Randagodron/hot-silicon-fuzz/export/sig_01_01.PNG

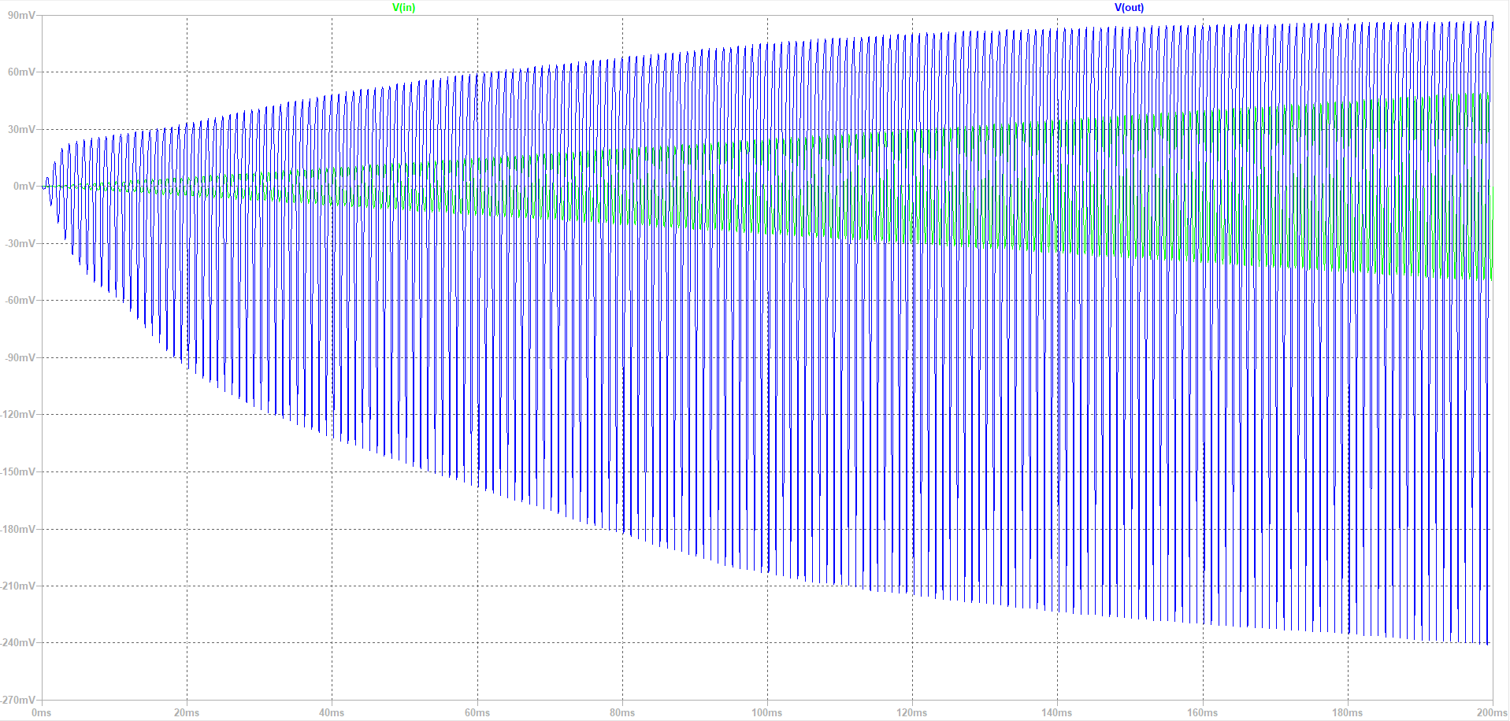
export/sig_01_01.PNG
