Randagodron/hot-silicon-fuzz/export/sig_01_02.PNG

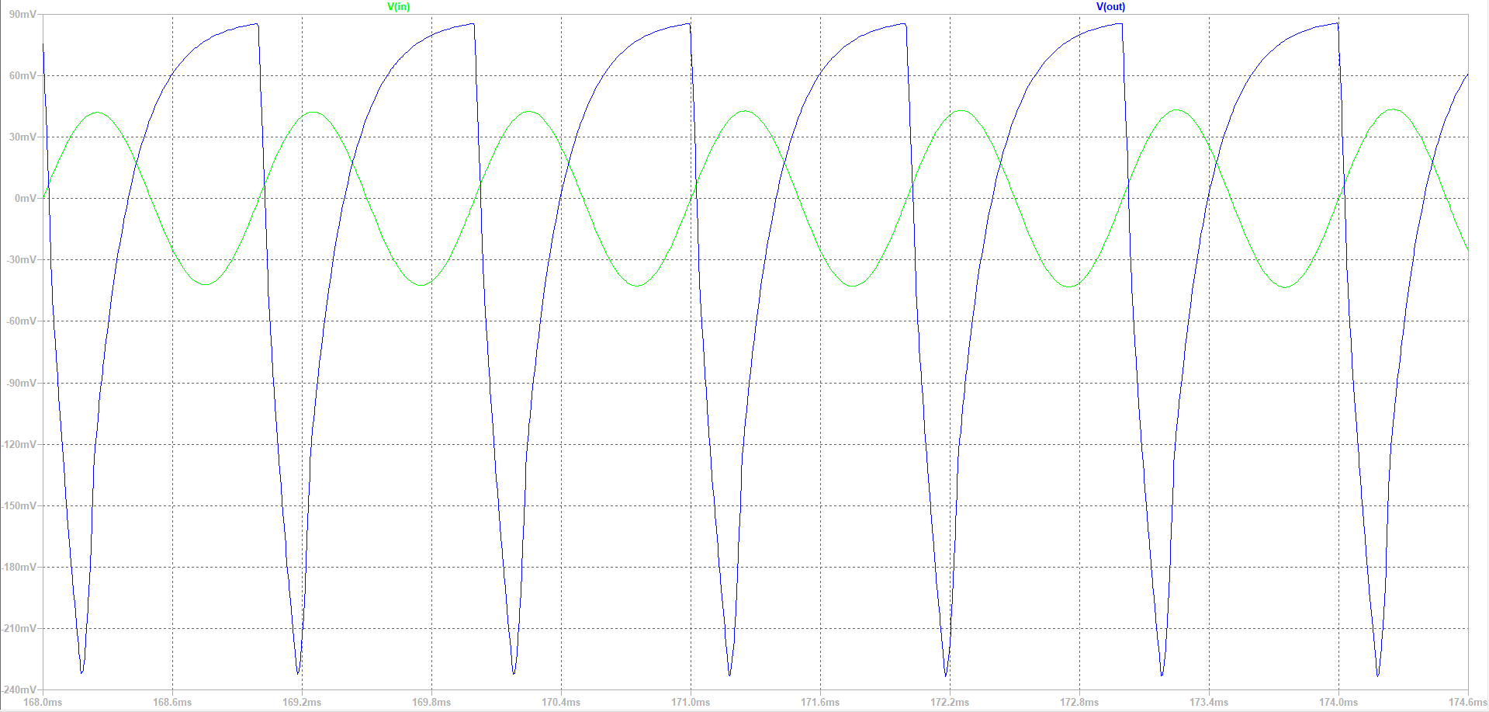
export/sig_01_02.PNG
