Randagodron/hot-silicon-fuzz/export/sig_02_02_bias0.1.PNG

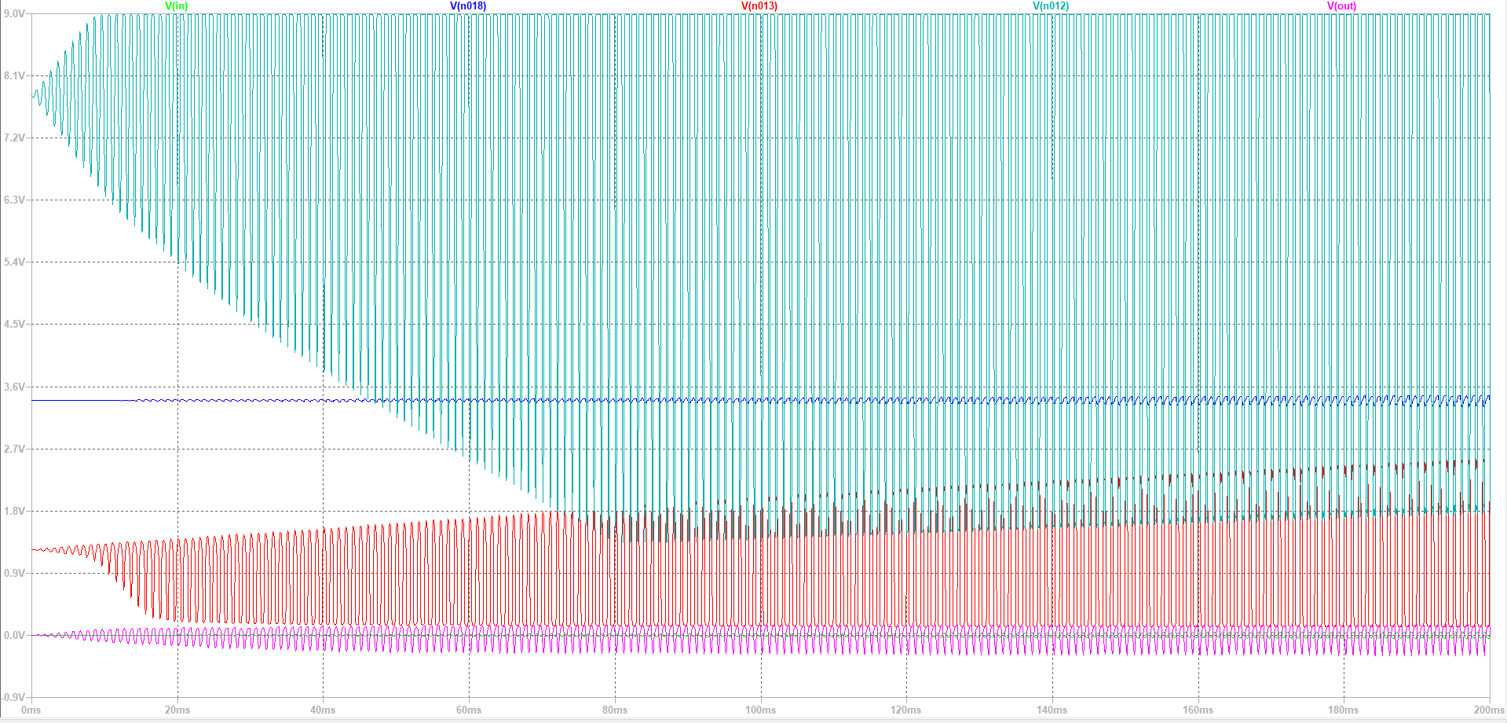
export/sig_02_02_bias0.1.PNG
