Randagodron/hot-silicon-fuzz/export/sig_02_03.PNG

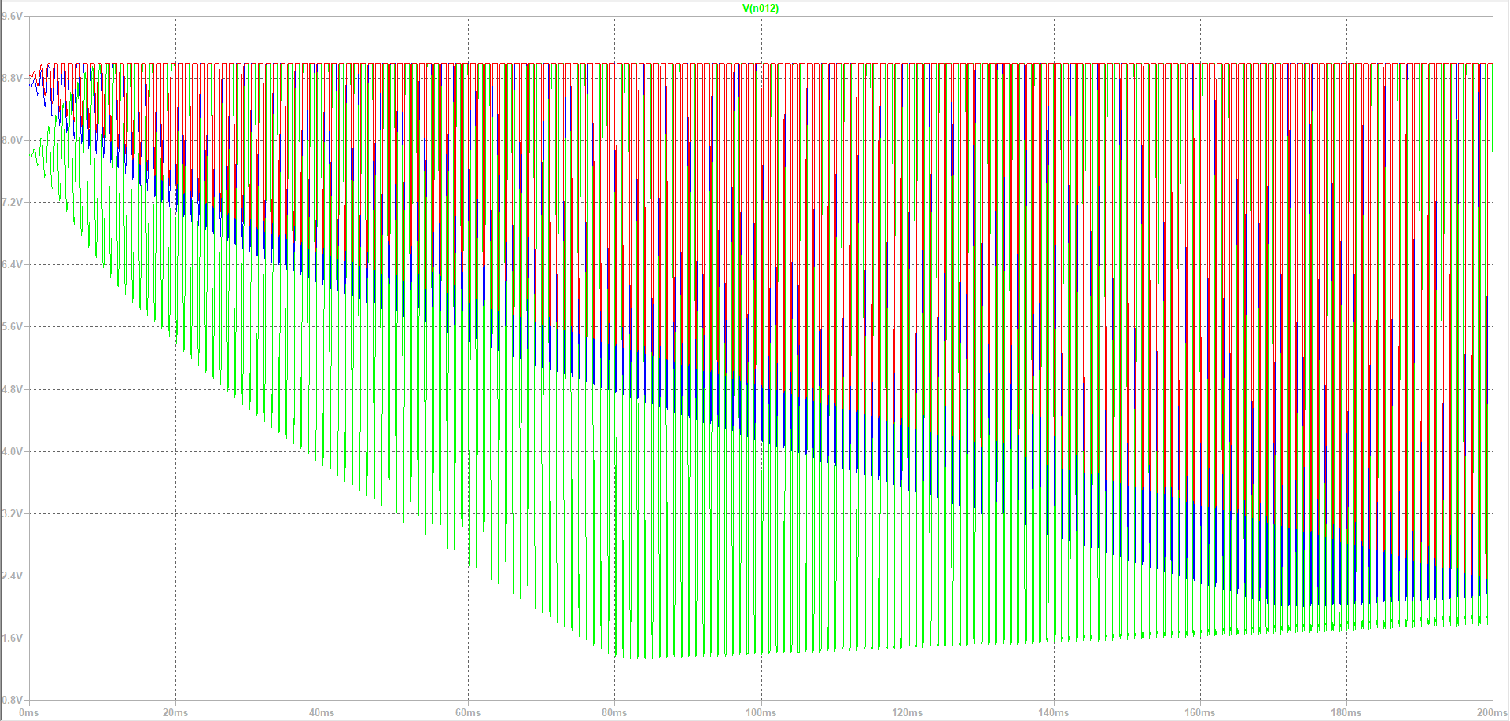
export/sig_02_03.PNG
