Randagodron/hot-silicon-fuzz/export/sig_02_04.PNG

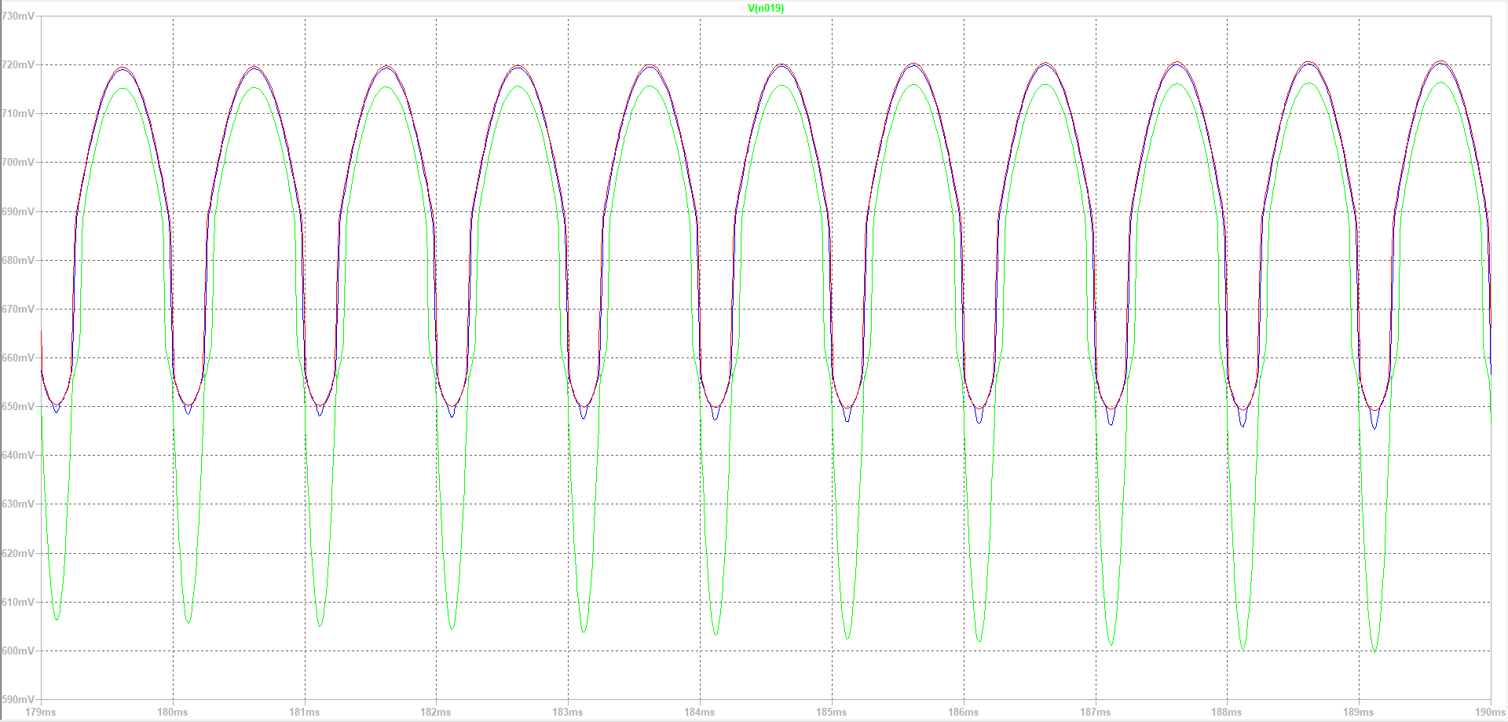
export/sig_02_04.PNG
