Randagodron/hot-silicon-fuzz/export/sig_02_06.PNG

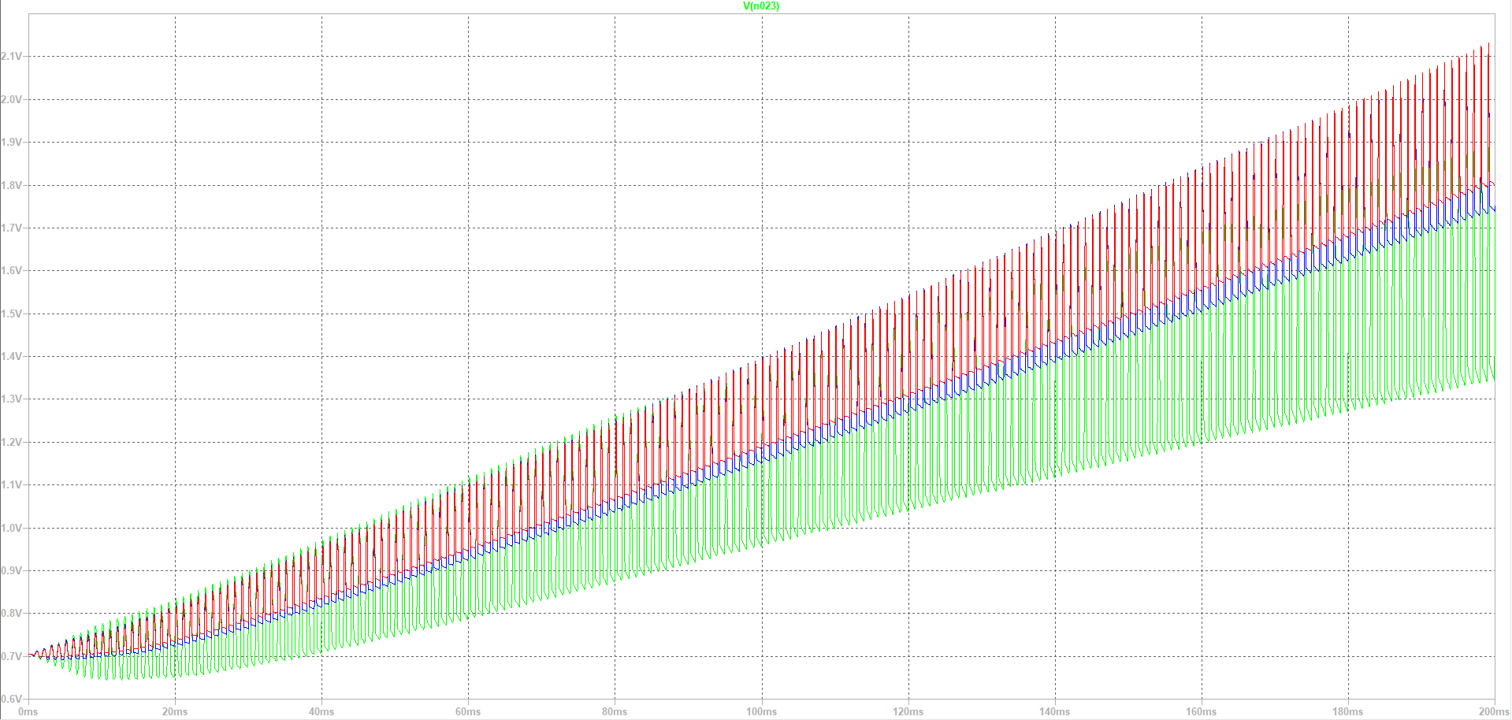
export/sig_02_06.PNG
