Randagodron/hot-silicon-fuzz/export/sig_03_02_character.PNG

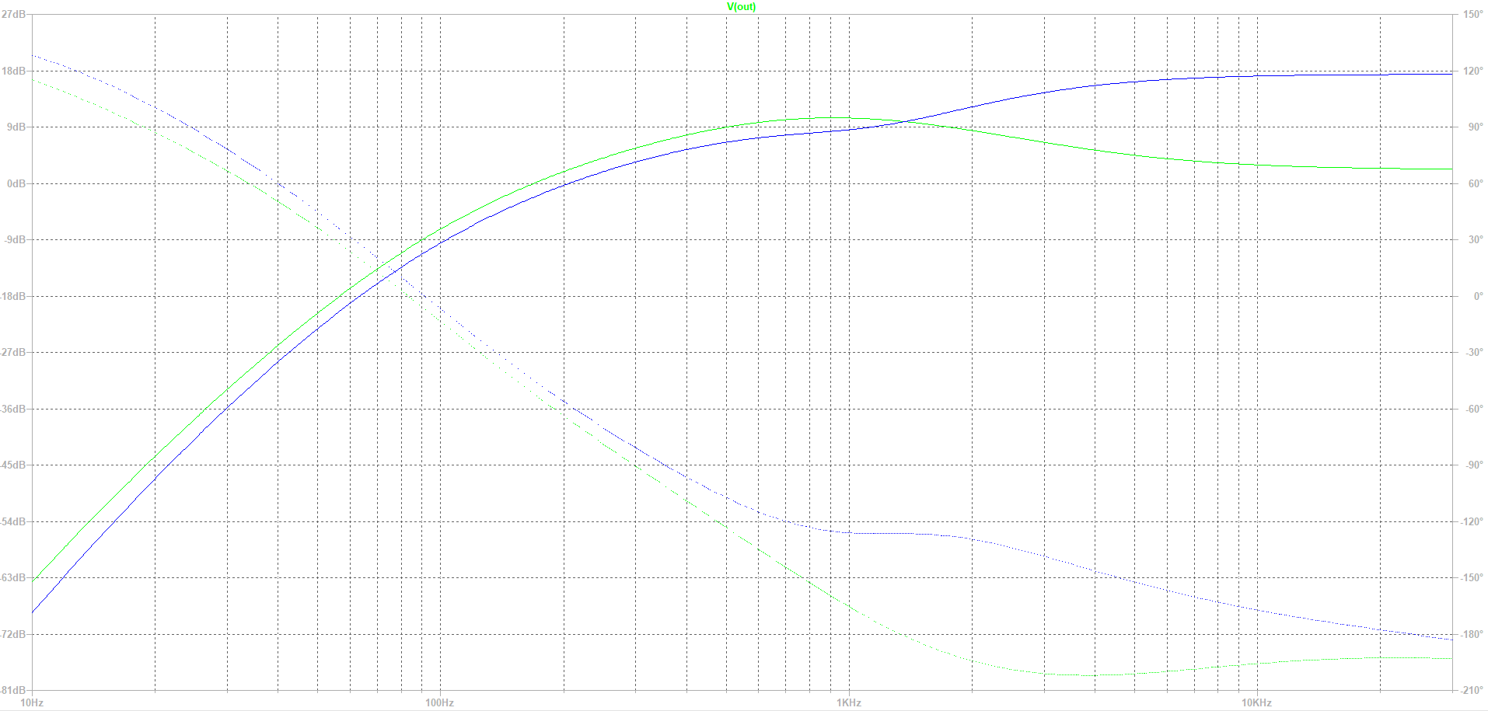
export/sig_03_02_character.PNG
