Randagodron/hot-silicon-fuzz/export/sig_04_01.PNG

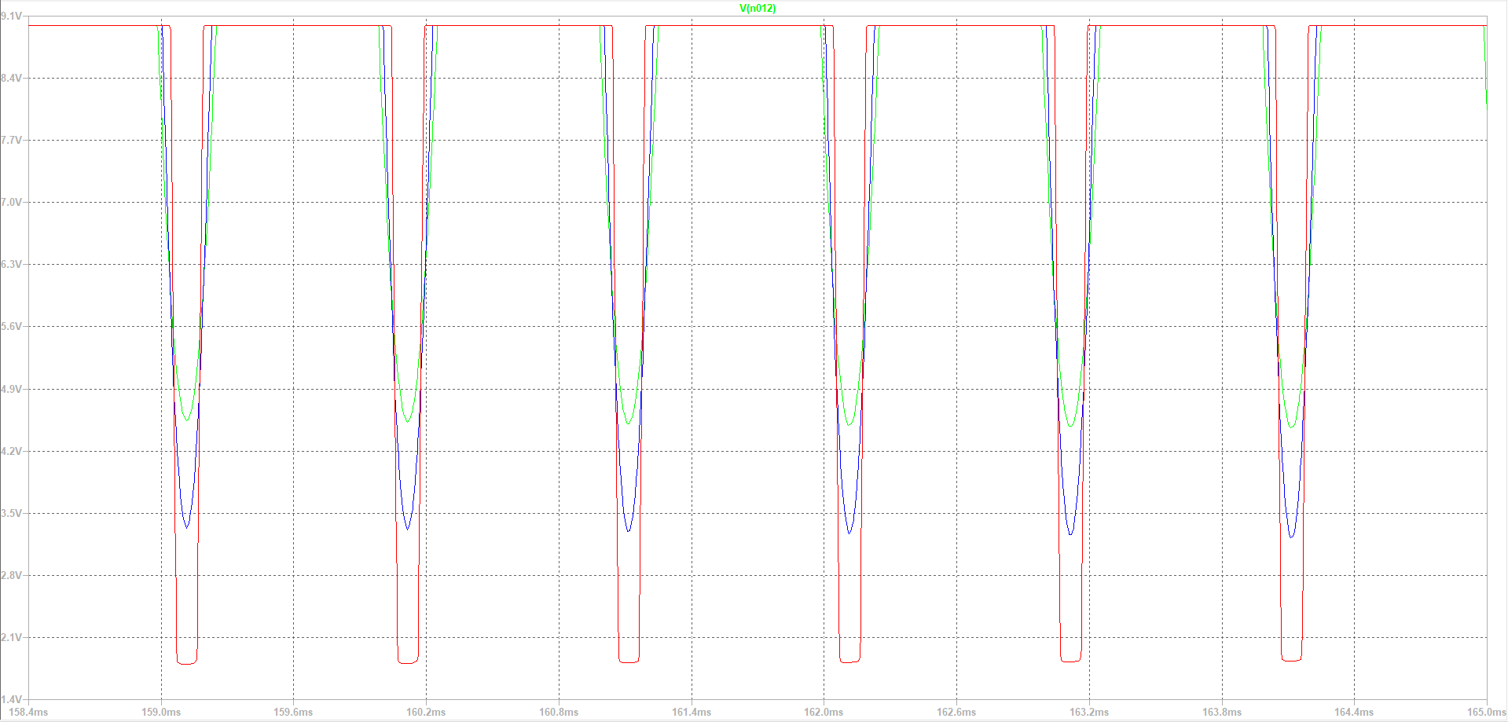
export/sig_04_01.PNG
