Randagodron/hot-silicon-fuzz/export/sig_04_02.PNG

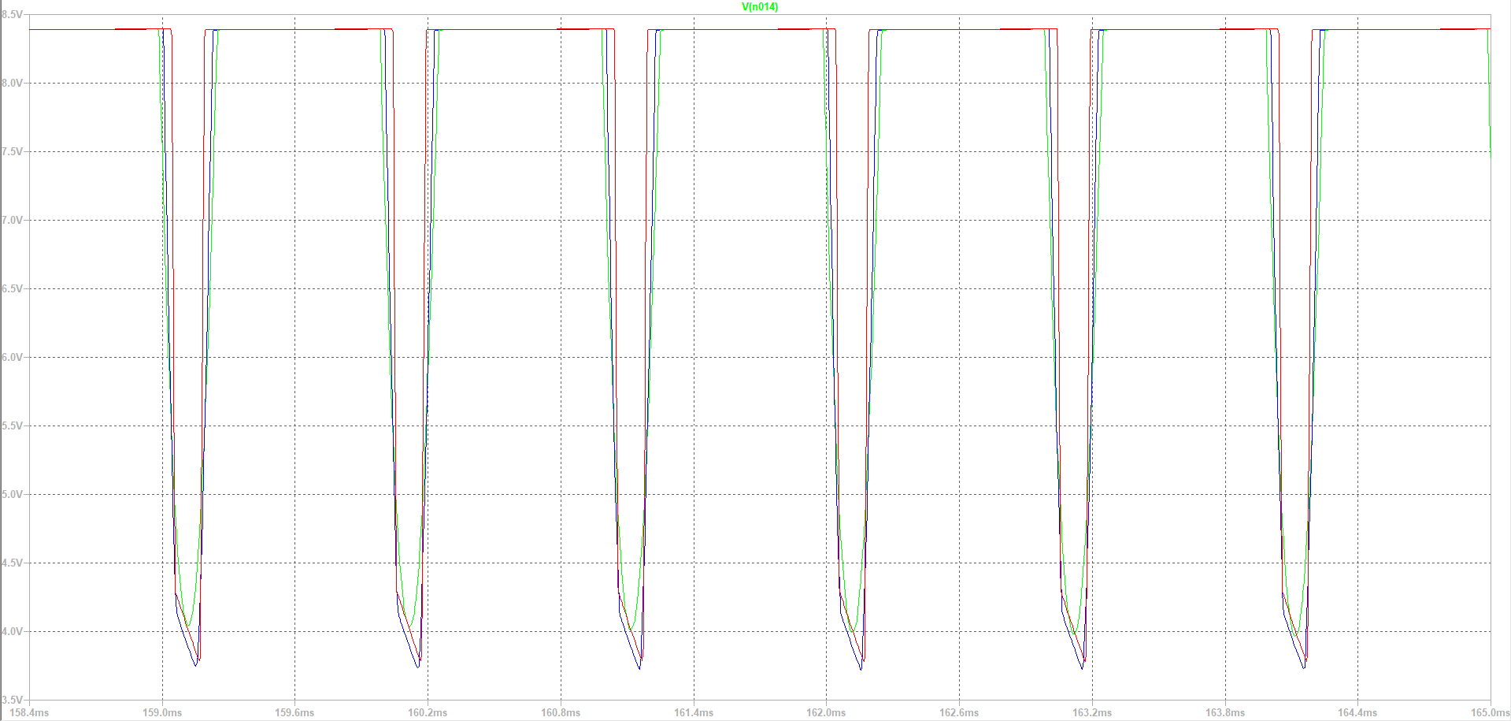
export/sig_04_02.PNG
