Randagodron/hot-silicon-fuzz/simu/hot_silicon_04.asc

B1: bv; V=V(venv)*V(vsin)
B2: bv; V=FAT
B3: bv; V=1-FAT
B4: bv; V=CHARACTER
B5: bv; V=CHARACTER
B6: bv; V=1-CHARACTER
B7: bv; V=1-CHARACTER
C1: cap; 47µ
C2: cap; 10n
C3: cap; 10µ
C4: cap; 100n
C5: cap; 100n
C6: cap; 4n7
C7: cap; 4.7µ
C8: cap; 10n
C9: cap; 100n
Q1: npn; Qmmbt5089l
Q2: npn; Qmmbt5089l
Q3: npn; Qmmbt5089l
Q4: npn; Qmmbt5089l
R1: res; 150k
R2: res; 22k
R3: res; 10k
R4: res; 1k
R5: res; 47k
R6: res; 10k
R7: res; 100
R8: res; 10k
R9: res; R=1k*(1-GAIN)
R10: res; R=1k*GAIN
R11: res; R=50k*BIAS
R12: res; 10k
R13: res; 2k2
R14: res; 22k
R15: res; R=50k*(1-TONE)
R16: res; R=50k*TONE
R17: res; R=50k*(1-VOL)
R18: res; R=50k*VOL
R19: res; 33k
R20: res; 10k
S1: sw; myswitch
S2: sw; myswitch
S3: sw; myswitch
S4: sw; myswitch
S5: sw; myswitch
S6: sw; myswitch
V1: voltage; ""; AC 100m
V2: voltage; ""; wavefile=.\guit_sample_01.wav chan=0
VCC: voltage; 9
VIN_ENV: voltage; PWL(0 0 200m 1)
VIN_SIN: voltage; SINE(0 50m 1k)
Named nets: vcc, 0, out, vsin, venv, in
.param GAIN=0.5
.param VOL=0.3
.param TONE=0.5
.param BIAS=0.9
.tran 200m
;.wave .\\hot_silicon.wav 16 44100 V(out)
;.ac oct 20 10 30k
.MODEL Qmmbt5089l npn
+IS=1.84669e-13 BF=1409.89 NF=1.03708 VAF=12.3022
+IKF=0.119779 ISE=2.83298e-11 NE=2.69107 BR=29.9731
+NR=1.01645 VAR=33.0833 IKR=1.19779 ISC=1e-16
+NC=1.02359 RB=6.69269 IRB=0.1 RBM=0.1
+RE=0.210278 RC=1.05139 XTB=1.24777 XTI=3.77926
+EG=1.206 CJE=8.0829e-12 VJE=0.450872 MJE=0.339997
+TF=2.69028e-10 XTF=1000 VTF=1166.16 ITF=1.92317
+CJC=5.15052e-12 VJC=0.463816 MJC=0.363265 XCJC=0.829786
+FC=0.8 CJS=0 VJS=0.75 MJS=0.5
+TR=1e-07 PTF=0 KF=0 AF=1
.param FAT=0
.param CHARACTER=0
.model myswitch SW(Ron=0.001 Roff=100MEG Vt=0.5 Lser=0 Vser=0)
.step param GAIN list 0.01 0.5 0.99
