Randagodron/hot-silicon-fuzz/simu/hot_silicon_03.asc

C1: cap; 47µ
C2: cap; 10n
C3: cap; 10µ
C4: cap; 100n
C5: cap; 100n
C6: cap; 4n
C7: cap; 4.7µ
C8: cap; 10n
C9: cap; 100n
D1: diode
Q1: npn; Qmmbt5089l
Q2: npn; Qmmbt5089l
Q3: npn; Qmmbt5089l
Q4: npn; Qmmbt5089l
Q5: npn; Qmmbt5089l
R1: res; 150k
R2: res; 22k
R3: res; 10k
R4: res; 1k
R5: res; 47k
R6: res; 10k
R7: res; 100
R8: res; 10k
R9: res; {{1k*(1-GAIN)}}
R10: res; {1k*GAIN}
R11: res; {5k*BIAS}
R12: res; 10k
R13: res; 0
R14: res; 22k
R15: res; {50k*(1-TONE)}
R16: res; {50k*TONE}
R17: res; {100k*(1-VOL)}
R18: res; {100k*VOL}
R19: res; 33k
R20: res; 200k
R21: res; 68k
V1: voltage; ""; AC 100m
V2: voltage; ""; wavefile=.\guit_sample_01.wav chan=0
VCC: voltage; 9
VIN_SIN: voltage; SINE(0 100m 1k)
Named nets: vcc, 0, v_out
.param GAIN=0.5
.param VOL=0.3
.param TONE=0.5
.param BIAS=0.5
.tran 6
.wave .\\hot_silicon.wav 16 44100 V(v_out)
;.ac oct 20 10 30k
.MODEL Qmmbt5089l npn
+IS=1.84669e-13 BF=1409.89 NF=1.03708 VAF=12.3022
+IKF=0.119779 ISE=2.83298e-11 NE=2.69107 BR=29.9731
+NR=1.01645 VAR=33.0833 IKR=1.19779 ISC=1e-16
+NC=1.02359 RB=6.69269 IRB=0.1 RBM=0.1
+RE=0.210278 RC=1.05139 XTB=1.24777 XTI=3.77926
+EG=1.206 CJE=8.0829e-12 VJE=0.450872 MJE=0.339997
+TF=2.69028e-10 XTF=1000 VTF=1166.16 ITF=1.92317
+CJC=5.15052e-12 VJC=0.463816 MJC=0.363265 XCJC=0.829786
+FC=0.8 CJS=0 VJS=0.75 MJS=0.5
+TR=1e-07 PTF=0 KF=0 AF=1
