Randagodron/hot-silicon-fuzz/simu/hot_silicon_01.asc

C1: cap; 47µ
C2: cap; 10n
C3: cap; 10µ
C4: cap; 100n
C5: cap; 100n
C6: cap; 100n
C7: cap; 4.7µ
C8: cap; 10n
Q1: npn
Q2: npn
Q3: npn
Q4: npn
R1: res; 150k
R2: res; 22k
R3: res; 10k
R4: res; 1k
R5: res; 47k
R6: res; 10k
R7: res; 100
R8: res; 10k
R9: res; {{1k*(1-GAIN)}}
R10: res; {1k*GAIN}
R11: res; {5k*BIAS}
R12: res; 10k
R13: res; 10k
R14: res; 2.2k
R15: res; {50k*(1-TONE)}
R16: res; {50k*TONE}
R17: res; {100k*(1-VOL)}
R18: res; {100k*VOL}
R19: res; 10k
V1: voltage; ""; AC 100m
V2: voltage; ""; wavefile=.\guit_sample_01.wav chan=0
VCC: voltage; 9
VIN_SIN: voltage; SINE(0 100m 1k)
Named nets: vcc, 0, v_out
.param GAIN=0.5
.param VOL=0.3
.param TONE=0.1
.param BIAS=0.5
;.tran 6
;.wave .\\hot_silicon.wav 16 44100 V(v_out)
.ac oct 20 10 30k
